ParqSystems/ParqHome/Home Automation/home_automation_frontend/assets/add-square-svgrepo-com.png

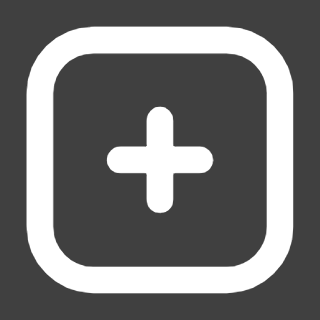
Home Automation/home_automation_frontend/assets/add-square-svgrepo-com.png
