ParqSystems/ParqHome/Home Automation/home_automation_frontend/assets/back-arrow-svgrepo-com.png

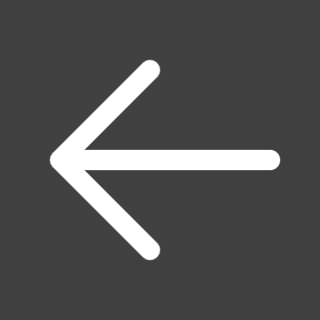
Home Automation/home_automation_frontend/assets/back-arrow-svgrepo-com.png
