ParqSystems/ParqHome/Home Automation/home_automation_frontend/assets/blue-fan-svgrepo-com.png

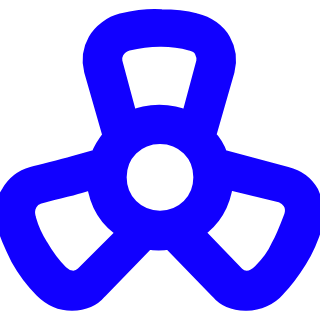
Home Automation/home_automation_frontend/assets/blue-fan-svgrepo-com.png
