ParqSystems/ParqHome/Home Automation/home_automation_frontend/assets/blue-fan.png

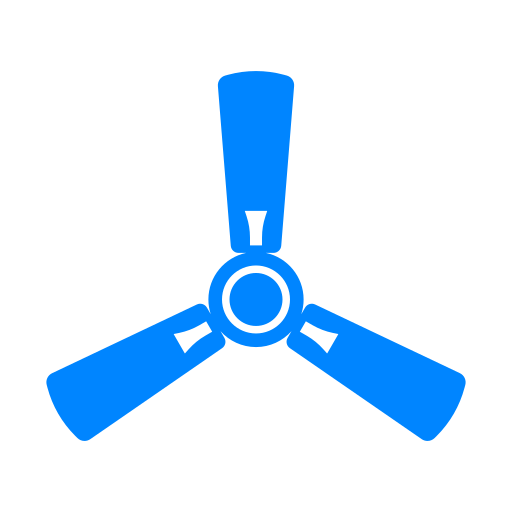
Home Automation/home_automation_frontend/assets/blue-fan.png
