ParqSystems/ParqHome/Home Automation/home_automation_frontend/assets/cross-svgrepo-com.png

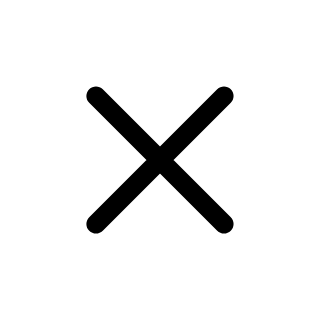
Home Automation/home_automation_frontend/assets/cross-svgrepo-com.png
