ParqSystems/ParqHome/Home Automation/home_automation_frontend/assets/edit-pencil-svgrepo-com.png

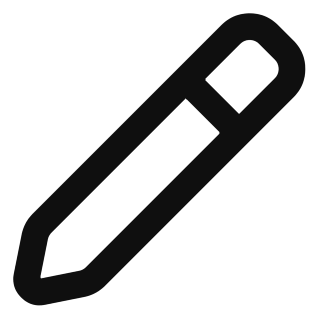
Home Automation/home_automation_frontend/assets/edit-pencil-svgrepo-com.png
