ParqSystems/ParqHome/Home Automation/home_automation_frontend/assets/email-svgrepo-com.png

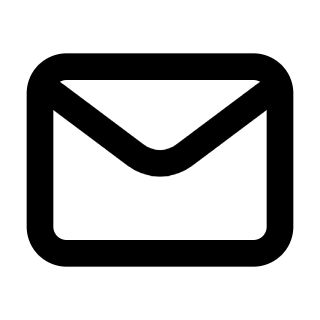
Home Automation/home_automation_frontend/assets/email-svgrepo-com.png
