ParqSystems/ParqHome/Home Automation/home_automation_frontend/assets/eye-slash-svgrepo-com.png

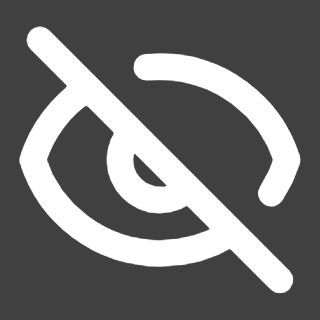
Home Automation/home_automation_frontend/assets/eye-slash-svgrepo-com.png
