ParqSystems/ParqHome/Home Automation/home_automation_frontend/assets/eye-svgrepo-com.png

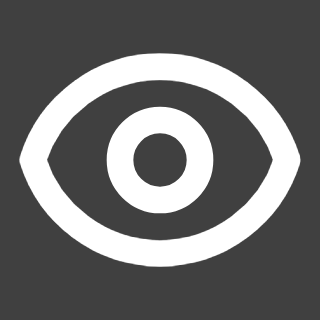
Home Automation/home_automation_frontend/assets/eye-svgrepo-com.png
