ParqSystems/ParqHome/Home Automation/home_automation_frontend/assets/google_without_bg.png

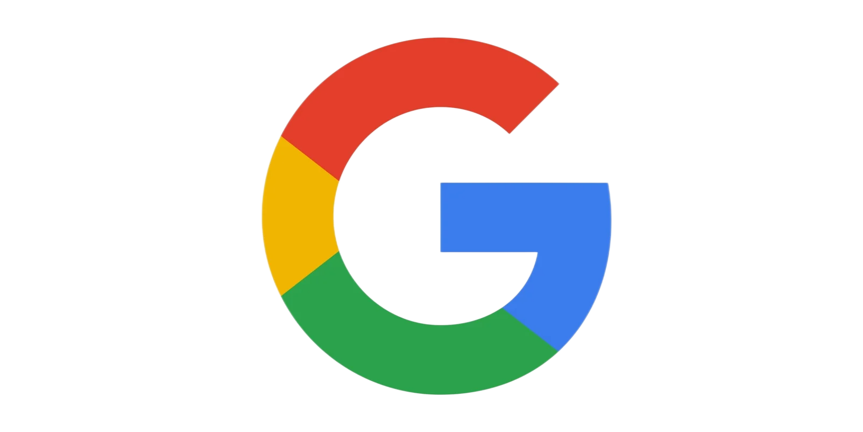
Home Automation/home_automation_frontend/assets/google_without_bg.png
