ParqSystems/ParqHome/Home Automation/home_automation_frontend/assets/image.png

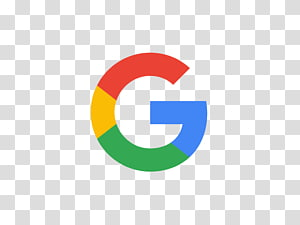
Home Automation/home_automation_frontend/assets/image.png
