ParqSystems/ParqHome/Home Automation/home_automation_frontend/assets/ParqSystems-blackbg.jpeg

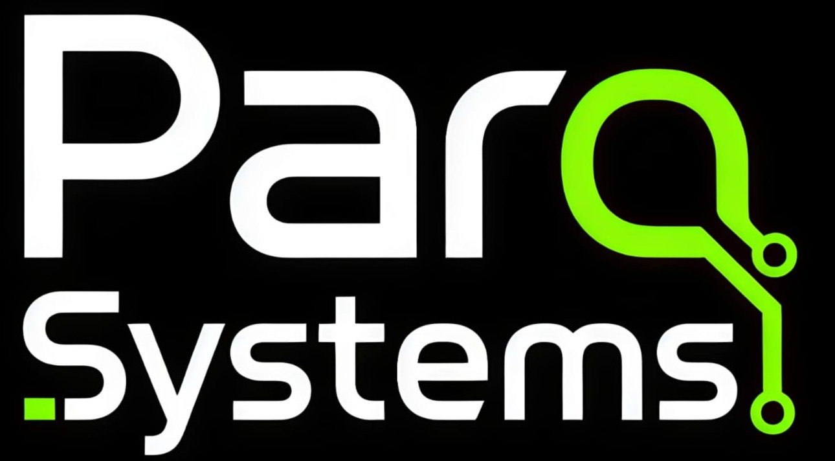
Home Automation/home_automation_frontend/assets/ParqSystems-blackbg.jpeg
