ParqSystems/ParqHome/Home Automation/home_automation_frontend/assets/ParqSystems-full-blackbg.jpeg

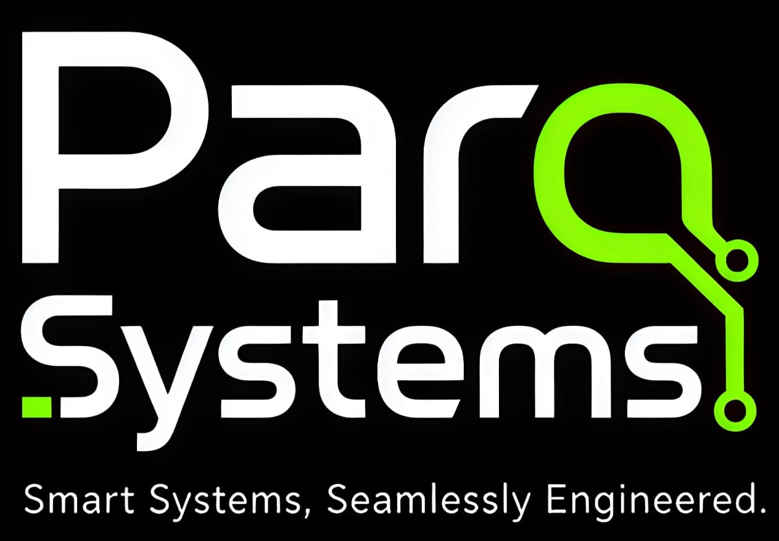
Home Automation/home_automation_frontend/assets/ParqSystems-full-blackbg.jpeg
