ParqSystems/ParqHome/Home Automation/home_automation_frontend/assets/ParqSystems-whitebg.jpeg

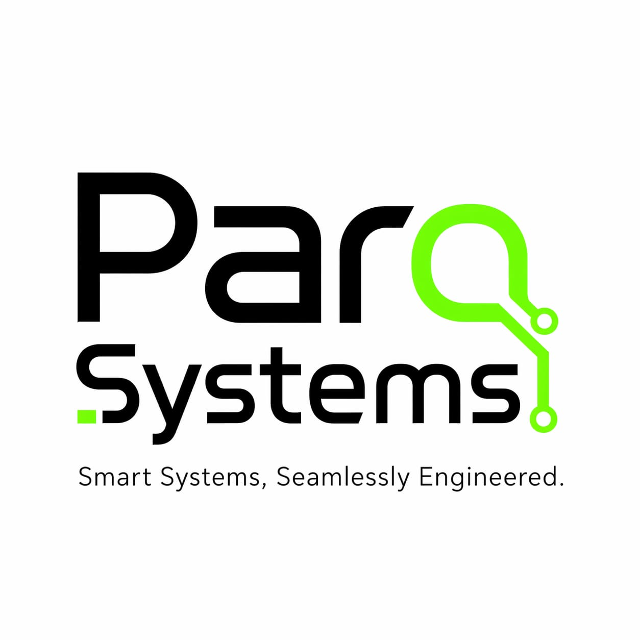
Home Automation/home_automation_frontend/assets/ParqSystems-whitebg.jpeg
