ParqSystems/ParqHome/Home Automation/home_automation_frontend/assets/phone-svgrepo-com.png

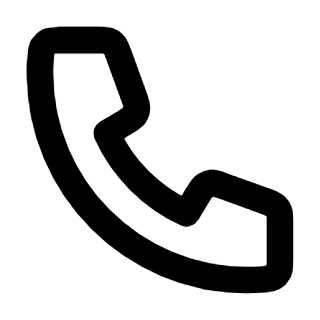
Home Automation/home_automation_frontend/assets/phone-svgrepo-com.png
