ParqSystems/ParqHome/Screenshot 2026-05-18 205648.png

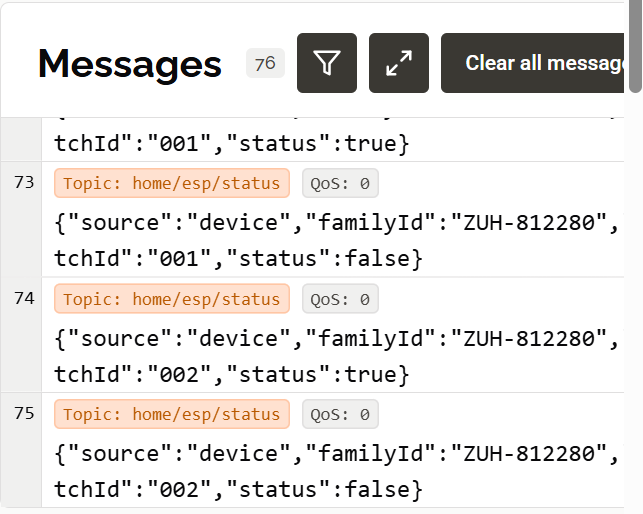
Screenshot 2026-05-18 205648.png
