ParqSystems/ParqHome/Screenshot 2026-05-18 205745.png

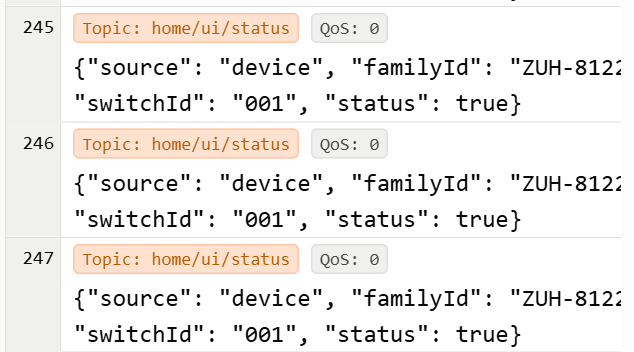
Screenshot 2026-05-18 205745.png
