ParqSystems/ParqHome/Screenshot 2026-05-18 205900.png

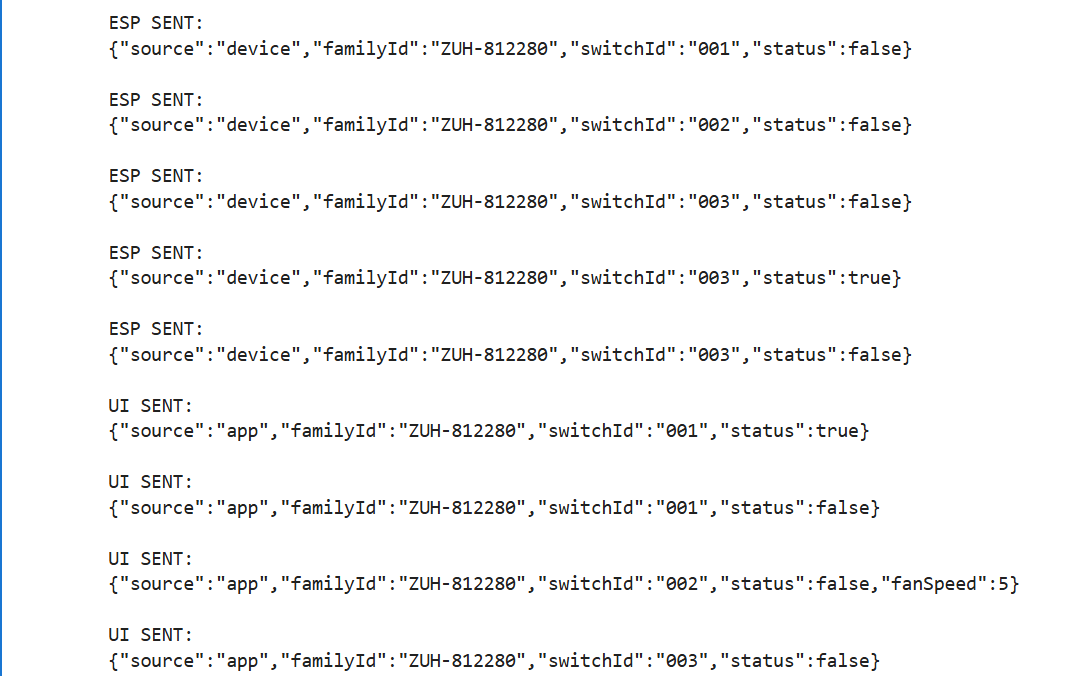
Screenshot 2026-05-18 205900.png
