ParqSystems/ParqHome/Screenshot 2026-05-19 181420.png

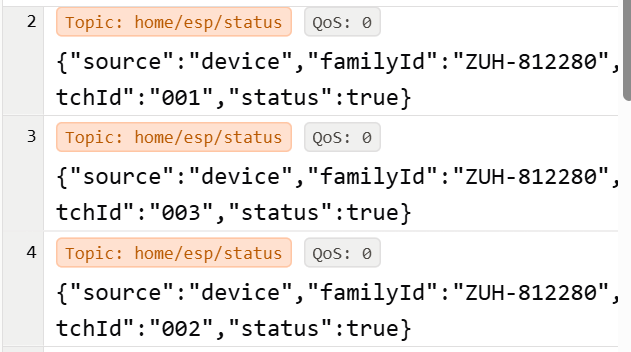
Screenshot 2026-05-19 181420.png
