ParqSystems/ParqHome/Screenshot 2026-05-19 181554.png

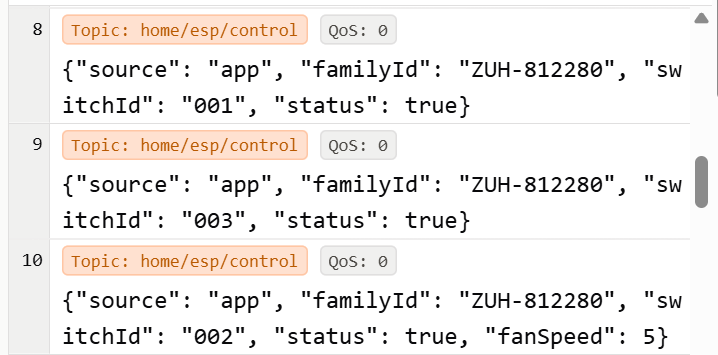
Screenshot 2026-05-19 181554.png
