ParqSystems/ParqHome/Screenshot 2026-05-19 181743.png

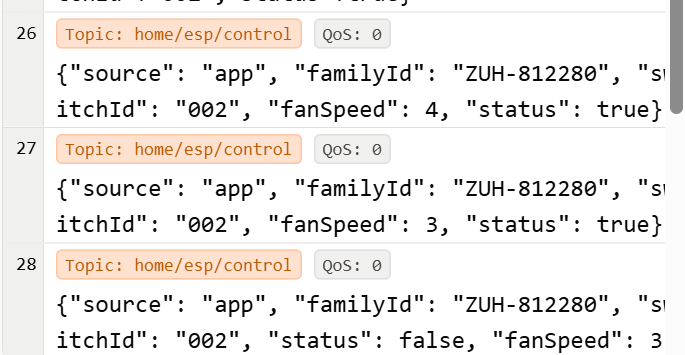
Screenshot 2026-05-19 181743.png
