ParqSystems/ParqHome/Screenshot 2026-05-19 181959.png

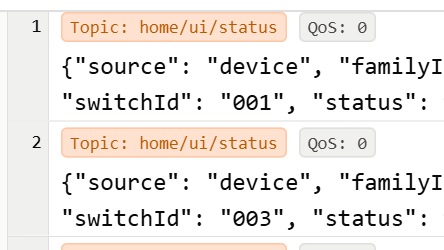
Screenshot 2026-05-19 181959.png
