ParqSystems/ParqHome/Screenshot 2026-05-19 182508.png

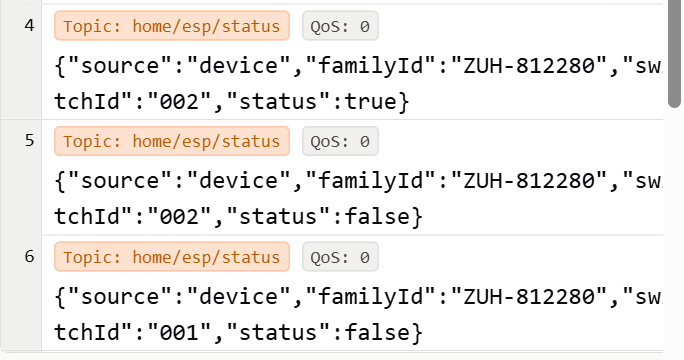
Screenshot 2026-05-19 182508.png
