ParqSystems/ParqHome/Screenshot 2026-05-19 182635.png

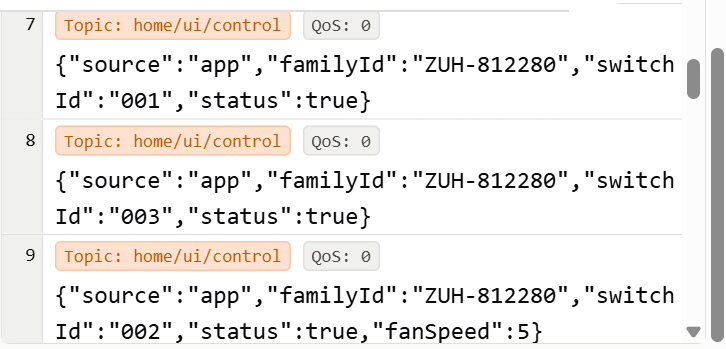
Screenshot 2026-05-19 182635.png
